medialab-prado/interactivos17-relatosenlaespera/2-2 Caso a estudiar/Resumen de datos observados (2).JPG

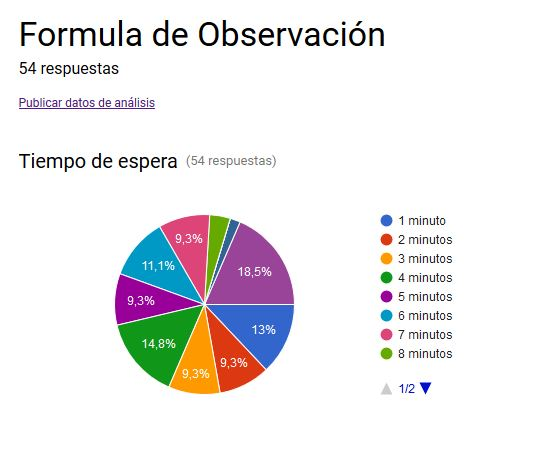
2-2 Caso a estudiar/Resumen de datos observados (2).JPG
