medialab-prado/interactivos17-relatosenlaespera/2-2 Caso a estudiar/Resumen de datos observados (3).JPG

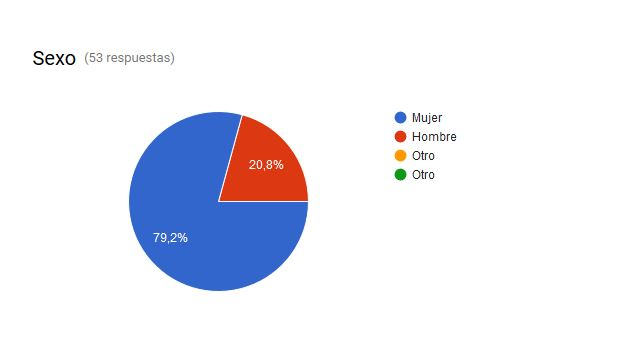
2-2 Caso a estudiar/Resumen de datos observados (3).JPG
