medialab-prado/interactivos17-relatosenlaespera/2-2 Caso a estudiar/Resumen de datos observados (7).JPG

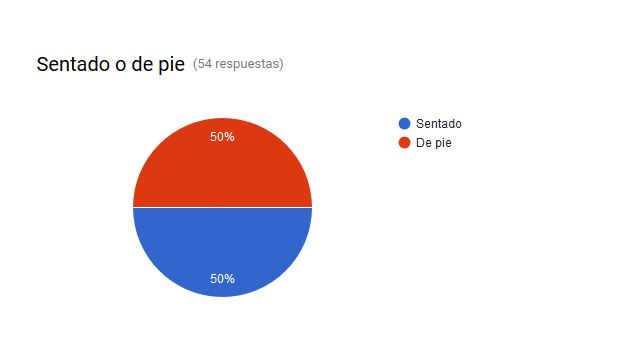
2-2 Caso a estudiar/Resumen de datos observados (7).JPG
