medialab-prado/interactivos17-relatosenlaespera/2-2 Caso a estudiar/Sobre el tiempo de espera (1).JPG

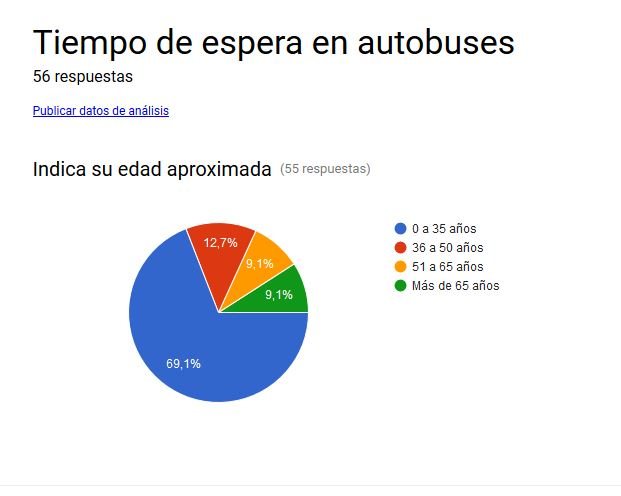
2-2 Caso a estudiar/Sobre el tiempo de espera (1).JPG
