medialab-prado/interactivos17-relatosenlaespera/3 Desarrollo de los relatos/Interpretes.jpg

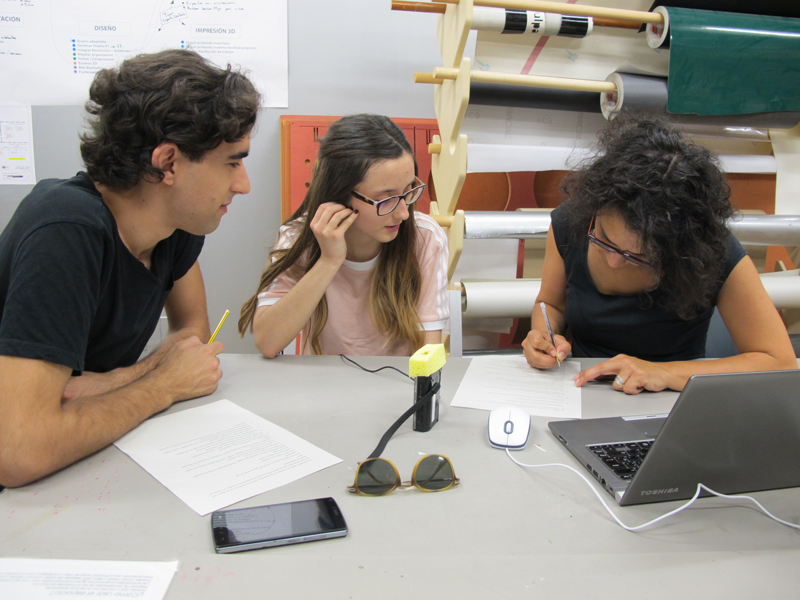
3 Desarrollo de los relatos/Interpretes.jpg
