medialab-prado/interactivos17-relatosenlaespera/4-Tecnologia/sensor.jpg

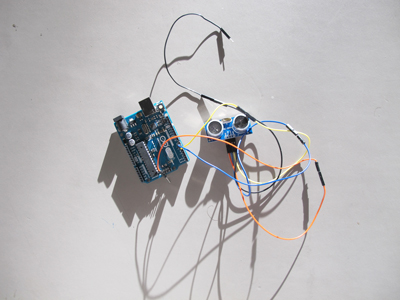
4-Tecnologia/sensor.jpg
