medialab-prado/interactivos17-relatosenlaespera/6-Dise-o de producto/atlas.jpg

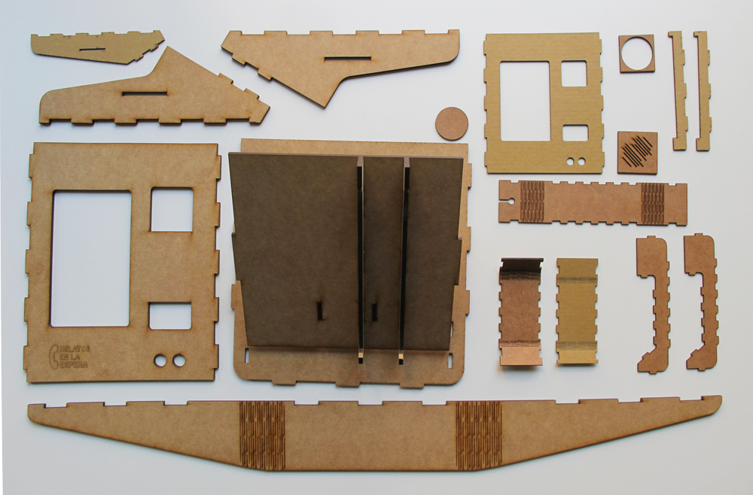
6-Dise-o de producto/atlas.jpg
