medialab-prado/interactivos17-relatosenlaespera/6-Dise-o de producto/Captura-1.jpg

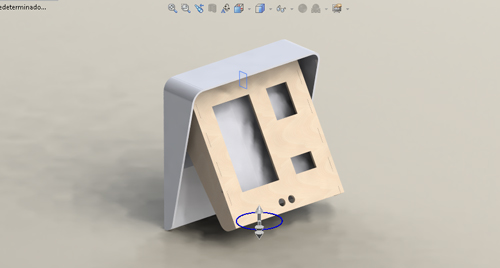
6-Dise-o de producto/Captura-1.jpg
