medialab-prado/interactivos17-relatosenlaespera/6-Dise-o de producto/proceso.jpg

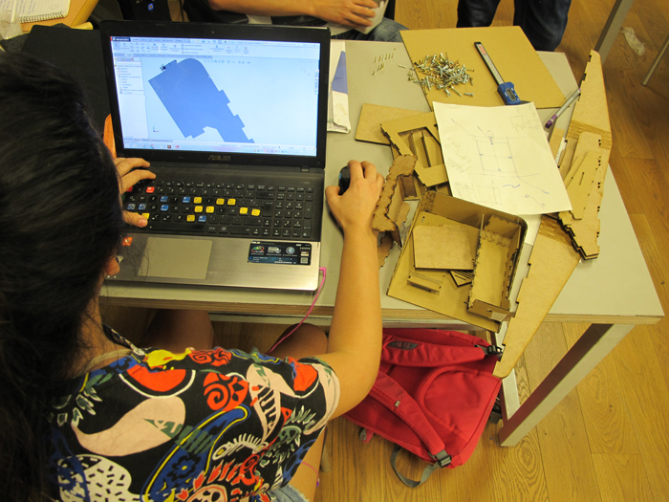
6-Dise-o de producto/proceso.jpg
