medialab-prado/interactivos17-relatosenlaespera/6-Dise-o de producto/prueba.jpg

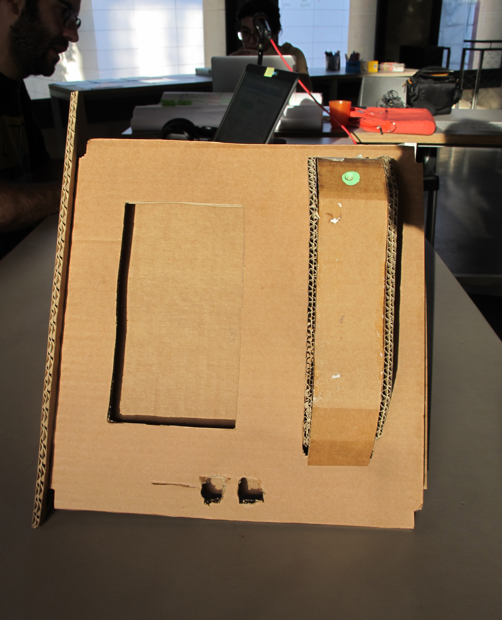
6-Dise-o de producto/prueba.jpg
